CuriousTech/Smart-Universal-Remote/URemote/screensavers.h

#ifndef SCREENSAVERS_H
#define SCREENSAVERS_H

#include <Arduino.h>
#include <TFT_eSPI.h>

enum Saver
{
  SS_Lines,
  SS_Bubbles,
  SS_Starfield,
  SS_Count, // Last one
};

struct Line
{
  int16_t x1;
  int16_t y1;
  int16_t x2;
  int16_t y2;
};

struct Bubble
{
  int16_t x;
  int16_t y;
  int8_t dx;
  int8_t dy;
  int8_t is;
  int16_t bsize;
  int16_t color;
};

struct Star
{
  float x;
  float y;
  float dx;
  float dy;
  uint8_t z;
};

class ScreenSavers
{
#define LINES 50
#define BUBBLES 10
#define STARS 80
#define BUFFER_SIZE 2048

static_assert( (sizeof(Bubble) * BUBBLES) < BUFFER_SIZE, "m_buffer size too small");
static_assert( (sizeof(Line) * LINES) < BUFFER_SIZE, "m_buffer size too small");
static_assert( (sizeof(Star) * STARS) < BUFFER_SIZE, "m_buffer size too small");

public:
  ScreenSavers(){};
  void init(uint16_t w, uint16_t h);
  void select(int n);
  void run(void);
  uint8_t m_saver;
  uint8_t hourFormat12(uint8_t h);
  const char *monthShortStr(uint8_t m);
  const char *monthStr(uint8_t m);
  const char *dayShortStr(uint8_t m);
  String localTimeString();

private:
  void Lines(bool bInit);
  void Bubbles(bool bInit);
  void resetBubble(Bubble& bubble);
  void Starfield(bool bInit);
  void resetStar(Star& star);

  uint16_t m_nDisplayWidth;
  uint16_t m_nDisplayHeight;

  uint8_t m_buffer[BUFFER_SIZE];
};

#endif // SCREENSAVERS_H
